ruediste/battery-analyzer/firmware/src/batteryChannelHal_arduino.cpp

#include "config.h"

#if IS_FRAMEWORK_ARDUINO
#include "batteryChannelHal.h"
#include "utils.h"
#include "batteryChannel.h"
#include <Arduino.h>

#if IS_STM
#include <stm32f1xx_ll_tim.h>
#include "stm32f1xx_ll_bus.h"
#endif

void BatteryChannelHal::loop()
{
}

#if IS_AVR
void BatteryChannelHal::setOutputPWM(uint16_t value)
{
  switch (channel)
  {
  case 0:
    OCR1A = value;
    break;
  case 1:
    OCR1B = value;
    break;
  }
}
uint16_t BatteryChannelHal::readVoltage()
{
  // A0/A1

  // select ADC channel with safety mask
  ADMUX = (ADMUX & 0xF0) | (channel & 0x0F);

  // single conversion mode
  ADCSRA |= (1 << ADSC);

  // wait until ADC conversion is complete
  while (ADCSRA & (1 << ADSC))
    ;

  return ADC << 6;
}

void BatteryChannelHal::init()
{
  OCR1A = 0; // clear PWM output
  OCR1B = 0; // clear PWM output

  DDRB |= _BV(PB1) | _BV(PB2);                  // Set pins as outputs (PB1/D9)
  TCCR1A = _BV(COM1A1) | _BV(COM1B1)            // Non-Inv PWM
           | _BV(WGM11);                        // Mode 14: Fast PWM, TOP=ICR1
  TCCR1B = _BV(WGM13) | _BV(WGM12) | _BV(CS10); // Prescaler 1
  ICR1 = 0xffff;                                // TOP counter value (Relieving OCR1A*)

  // adc initialization
  // Select Vref=AVcc
  ADMUX |= (1 << REFS0);

  // set prescaller to 128 and enable ADC (16MHz/128 => 125kHz (should be in range 50kHz to 200 kHz))
  ADCSRA |= (1 << ADPS2) | (1 << ADPS1) | (1 << ADPS0) | (1 << ADEN);
}
#endif

#if IS_STM

TIM_HandleTypeDef htim1;
TIM_HandleTypeDef htim2;
TIM_HandleTypeDef htim3;

void HAL_TIM_MspPostInit(TIM_HandleTypeDef *htim)
{
  GPIO_InitTypeDef GPIO_InitStruct = {0};
  if (htim->Instance == TIM1)
  {
    __HAL_RCC_GPIOA_CLK_ENABLE();
    /**TIM1 GPIO Configuration
    PA8     ------> TIM1_CH1
    PA9     ------> TIM1_CH2
    PA10     ------> TIM1_CH3
    */
    GPIO_InitStruct.Pin = GPIO_PIN_8 | GPIO_PIN_9 | GPIO_PIN_10;
    GPIO_InitStruct.Mode = GPIO_MODE_AF_PP;
    GPIO_InitStruct.Speed = GPIO_SPEED_FREQ_LOW;
    HAL_GPIO_Init(GPIOA, &GPIO_InitStruct);

  }
  else if (htim->Instance == TIM2)
  {
    __HAL_RCC_GPIOB_CLK_ENABLE();
    __HAL_RCC_GPIOA_CLK_ENABLE();
    /**TIM2 GPIO Configuration
    PB10     ------> TIM2_CH3
    PB11     ------> TIM2_CH4
    PA15     ------> TIM2_CH1
    PB3     ------> TIM2_CH2
    */
    GPIO_InitStruct.Pin = GPIO_PIN_10 | GPIO_PIN_11 | GPIO_PIN_3;
    GPIO_InitStruct.Mode = GPIO_MODE_AF_PP;
    GPIO_InitStruct.Speed = GPIO_SPEED_FREQ_LOW;
    HAL_GPIO_Init(GPIOB, &GPIO_InitStruct);

    GPIO_InitStruct.Pin = GPIO_PIN_15;
    GPIO_InitStruct.Mode = GPIO_MODE_AF_PP;
    GPIO_InitStruct.Speed = GPIO_SPEED_FREQ_LOW;
    HAL_GPIO_Init(GPIOA, &GPIO_InitStruct);

    __HAL_AFIO_REMAP_TIM2_ENABLE();

  }
  else if (htim->Instance == TIM3)
  {
    __HAL_RCC_GPIOB_CLK_ENABLE();
    /**TIM3 GPIO Configuration
    PB1     ------> TIM3_CH4
    PB4     ------> TIM3_CH1
    */
    GPIO_InitStruct.Pin = GPIO_PIN_1 | GPIO_PIN_4;
    GPIO_InitStruct.Mode = GPIO_MODE_AF_PP;
    GPIO_InitStruct.Speed = GPIO_SPEED_FREQ_LOW;
    HAL_GPIO_Init(GPIOB, &GPIO_InitStruct);

    __HAL_AFIO_REMAP_TIM3_PARTIAL();

  }
}

/**
 * @brief TIM1 Initialization Function
 * @param None
 * @retval None
 */
static void MX_TIM1_Init(void)
{

  TIM_ClockConfigTypeDef sClockSourceConfig = {0};
  TIM_MasterConfigTypeDef sMasterConfig = {0};
  TIM_OC_InitTypeDef sConfigOC = {0};
  TIM_BreakDeadTimeConfigTypeDef sBreakDeadTimeConfig = {0};

  htim1.Instance = TIM1;
  htim1.Init.Prescaler = 0;
  htim1.Init.CounterMode = TIM_COUNTERMODE_UP;
  htim1.Init.Period = BatteryChannelHal::MAX_PWM;
  htim1.Init.ClockDivision = TIM_CLOCKDIVISION_DIV1;
  htim1.Init.RepetitionCounter = 0;
  htim1.Init.AutoReloadPreload = TIM_AUTORELOAD_PRELOAD_ENABLE;
  if (HAL_TIM_Base_Init(&htim1) != HAL_OK)
  {
    Error_Handler();
  }
  sClockSourceConfig.ClockSource = TIM_CLOCKSOURCE_INTERNAL;
  if (HAL_TIM_ConfigClockSource(&htim1, &sClockSourceConfig) != HAL_OK)
  {
    Error_Handler();
  }
  if (HAL_TIM_PWM_Init(&htim1) != HAL_OK)
  {
    Error_Handler();
  }
  sMasterConfig.MasterOutputTrigger = TIM_TRGO_RESET;
  sMasterConfig.MasterSlaveMode = TIM_MASTERSLAVEMODE_DISABLE;
  if (HAL_TIMEx_MasterConfigSynchronization(&htim1, &sMasterConfig) != HAL_OK)
  {
    Error_Handler();
  }
  sConfigOC.OCMode = TIM_OCMODE_PWM1;
  sConfigOC.Pulse = 0;
  sConfigOC.OCPolarity = TIM_OCPOLARITY_HIGH;
  sConfigOC.OCNPolarity = TIM_OCNPOLARITY_HIGH;
  sConfigOC.OCFastMode = TIM_OCFAST_DISABLE;
  sConfigOC.OCIdleState = TIM_OCIDLESTATE_RESET;
  sConfigOC.OCNIdleState = TIM_OCNIDLESTATE_RESET;
  if (HAL_TIM_PWM_ConfigChannel(&htim1, &sConfigOC, TIM_CHANNEL_1) != HAL_OK)
  {
    Error_Handler();
  }
  if (HAL_TIM_PWM_ConfigChannel(&htim1, &sConfigOC, TIM_CHANNEL_2) != HAL_OK)
  {
    Error_Handler();
  }
  if (HAL_TIM_PWM_ConfigChannel(&htim1, &sConfigOC, TIM_CHANNEL_3) != HAL_OK)
  {
    Error_Handler();
  }
  sBreakDeadTimeConfig.OffStateRunMode = TIM_OSSR_DISABLE;
  sBreakDeadTimeConfig.OffStateIDLEMode = TIM_OSSI_DISABLE;
  sBreakDeadTimeConfig.LockLevel = TIM_LOCKLEVEL_OFF;
  sBreakDeadTimeConfig.DeadTime = 0;
  sBreakDeadTimeConfig.BreakState = TIM_BREAK_DISABLE;
  sBreakDeadTimeConfig.BreakPolarity = TIM_BREAKPOLARITY_HIGH;
  sBreakDeadTimeConfig.AutomaticOutput = TIM_AUTOMATICOUTPUT_DISABLE;
  if (HAL_TIMEx_ConfigBreakDeadTime(&htim1, &sBreakDeadTimeConfig) != HAL_OK)
  {
    Error_Handler();
  }
  HAL_TIM_MspPostInit(&htim1);
}

/**
 * @brief TIM2 Initialization Function
 * @param None
 * @retval None
 */
static void MX_TIM2_Init(void)
{

  TIM_ClockConfigTypeDef sClockSourceConfig = {0};
  TIM_MasterConfigTypeDef sMasterConfig = {0};
  TIM_OC_InitTypeDef sConfigOC = {0};

  htim2.Instance = TIM2;
  htim2.Init.Prescaler = 0;
  htim2.Init.CounterMode = TIM_COUNTERMODE_UP;
  htim2.Init.Period = BatteryChannelHal::MAX_PWM;
  htim2.Init.ClockDivision = TIM_CLOCKDIVISION_DIV1;
  htim2.Init.AutoReloadPreload = TIM_AUTORELOAD_PRELOAD_ENABLE;
  if (HAL_TIM_Base_Init(&htim2) != HAL_OK)
  {
    Error_Handler();
  }
  sClockSourceConfig.ClockSource = TIM_CLOCKSOURCE_INTERNAL;
  if (HAL_TIM_ConfigClockSource(&htim2, &sClockSourceConfig) != HAL_OK)
  {
    Error_Handler();
  }
  if (HAL_TIM_PWM_Init(&htim2) != HAL_OK)
  {
    Error_Handler();
  }
  sMasterConfig.MasterOutputTrigger = TIM_TRGO_RESET;
  sMasterConfig.MasterSlaveMode = TIM_MASTERSLAVEMODE_DISABLE;
  if (HAL_TIMEx_MasterConfigSynchronization(&htim2, &sMasterConfig) != HAL_OK)
  {
    Error_Handler();
  }
  sConfigOC.OCMode = TIM_OCMODE_PWM1;
  sConfigOC.Pulse = 0;
  sConfigOC.OCPolarity = TIM_OCPOLARITY_HIGH;
  sConfigOC.OCFastMode = TIM_OCFAST_DISABLE;
  if (HAL_TIM_PWM_ConfigChannel(&htim2, &sConfigOC, TIM_CHANNEL_1) != HAL_OK)
  {
    Error_Handler();
  }
  if (HAL_TIM_PWM_ConfigChannel(&htim2, &sConfigOC, TIM_CHANNEL_2) != HAL_OK)
  {
    Error_Handler();
  }
  if (HAL_TIM_PWM_ConfigChannel(&htim2, &sConfigOC, TIM_CHANNEL_3) != HAL_OK)
  {
    Error_Handler();
  }
  if (HAL_TIM_PWM_ConfigChannel(&htim2, &sConfigOC, TIM_CHANNEL_4) != HAL_OK)
  {
    Error_Handler();
  }
  HAL_TIM_MspPostInit(&htim2);
}

/**
 * @brief TIM3 Initialization Function
 * @param None
 * @retval None
 */
static void MX_TIM3_Init(void)
{

  TIM_ClockConfigTypeDef sClockSourceConfig = {0};
  TIM_MasterConfigTypeDef sMasterConfig = {0};
  TIM_OC_InitTypeDef sConfigOC = {0};

  htim3.Instance = TIM3;
  htim3.Init.Prescaler = 0;
  htim3.Init.CounterMode = TIM_COUNTERMODE_UP;
  htim3.Init.Period = BatteryChannelHal::MAX_PWM;
  htim3.Init.ClockDivision = TIM_CLOCKDIVISION_DIV1;
  htim3.Init.AutoReloadPreload = TIM_AUTORELOAD_PRELOAD_ENABLE;
  if (HAL_TIM_Base_Init(&htim3) != HAL_OK)
  {
    Error_Handler();
  }
  sClockSourceConfig.ClockSource = TIM_CLOCKSOURCE_INTERNAL;
  if (HAL_TIM_ConfigClockSource(&htim3, &sClockSourceConfig) != HAL_OK)
  {
    Error_Handler();
  }
  if (HAL_TIM_PWM_Init(&htim3) != HAL_OK)
  {
    Error_Handler();
  }
  sMasterConfig.MasterOutputTrigger = TIM_TRGO_RESET;
  sMasterConfig.MasterSlaveMode = TIM_MASTERSLAVEMODE_DISABLE;
  if (HAL_TIMEx_MasterConfigSynchronization(&htim3, &sMasterConfig) != HAL_OK)
  {
    Error_Handler();
  }
  sConfigOC.OCMode = TIM_OCMODE_PWM1;
  sConfigOC.Pulse = 0;
  sConfigOC.OCPolarity = TIM_OCPOLARITY_HIGH;
  sConfigOC.OCFastMode = TIM_OCFAST_DISABLE;
  if (HAL_TIM_PWM_ConfigChannel(&htim3, &sConfigOC, TIM_CHANNEL_1) != HAL_OK)
  {
    Error_Handler();
  }
  if (HAL_TIM_PWM_ConfigChannel(&htim3, &sConfigOC, TIM_CHANNEL_4) != HAL_OK)
  {
    Error_Handler();
  }
  HAL_TIM_MspPostInit(&htim3);
}

// int BatteryChannelHal::pwmPins[] = {PA8, PA9, PB11, PB1, PA10, PA15, PB3, PB4};
int BatteryChannelHal::analogInPins[] = {PA0, PA1, PA2, PA3, PA4, PA5, PA6, PA7};

void BatteryChannelHal::setOutputPWM(uint16_t value)
{
  // analogWrite(pwmPins[channel], value);
  switch (channel)
  {
  case 0: // PA8
    htim1.Instance->CCR1 = value;
    break;
  case 1: // PA9
    htim1.Instance->CCR2 = value;
    break;
  case 2: // PB11
    htim2.Instance->CCR4 = value;
    break;
  case 3: // PB1
    htim3.Instance->CCR4 = value;
    break;
  case 4: // PA10
    htim1.Instance->CCR3 = value;
    break;
  case 5: // PA15
    htim2.Instance->CCR1 = value;
    break;
  case 6: // PB3
    htim2.Instance->CCR2 = value;
    break;
  case 7: // PB4
    htim3.Instance->CCR1 = value;
    break;
  }
}

uint16_t BatteryChannelHal::readVoltage()
{
  return analogRead(analogInPins[channel]);
}

void BatteryChannelHal::init()
{
  MX_TIM1_Init();
  MX_TIM2_Init();
  MX_TIM3_Init();

  HAL_TIM_PWM_Start(&htim1, TIM_CHANNEL_1);
  HAL_TIM_PWM_Start(&htim1, TIM_CHANNEL_2);
  HAL_TIM_PWM_Start(&htim2, TIM_CHANNEL_4);
  HAL_TIM_PWM_Start(&htim3, TIM_CHANNEL_4);
  HAL_TIM_PWM_Start(&htim1, TIM_CHANNEL_3);
  HAL_TIM_PWM_Start(&htim2, TIM_CHANNEL_1);
  HAL_TIM_PWM_Start(&htim2, TIM_CHANNEL_2);
  HAL_TIM_PWM_Start(&htim3, TIM_CHANNEL_1);

  // ref
  HAL_TIM_PWM_Start(&htim2, TIM_CHANNEL_3);
  htim2.Instance->CCR3 = MAX_PWM >> 1;

  // analogWriteFrequency(10000);
  // analogWriteResolution(12);

  analogReadResolution(16);

  // analogWrite(PB10, 0x400);
  // AFIO->MAPR2|=AFIO_MAPR_TIM2_REMAP_FULLREMAP;

  for (int i = 0; i < channelCount; i++)
    pinMode(analogInPins[i], INPUT_ANALOG);
  // for (int i = 0; i < channelCount; i++)
  //     pinMode(pwmPins[i], OUTPUT);
}
#endif
#endif
