ruediste/battery-analyzer/firmware/src/input_native.cpp

#define INPUT_CPP
#include "config.h"

#if IS_FRAMEWORK_NATIVE
#include "input.h"
#include "utils.h"

namespace input
{
  void init()
  {
    // NOOP
  }

  void loop()
  {
    // NOOP
  }
  void checkInputs()
  {
    // NOOP
  }

} // namespace Input

#endif
