ruediste/battery-analyzer/cubeMx/test.ioc

Mcu.UserName=STM32F103C8Tx
PA0-WKUP.Signal=ADCx_IN0
PA1.Signal=ADCx_IN1
PA10.Signal=S_TIM1_CH3
PA15.Signal=S_TIM2_CH1_ETR
PA2.Signal=ADCx_IN2
PA3.Signal=ADCx_IN3
PA4.Signal=ADCx_IN4
PA5.Signal=ADCx_IN5
PA6.Signal=ADCx_IN6
PA7.Signal=ADCx_IN7
PA8.Signal=S_TIM1_CH1
PA9.Signal=S_TIM1_CH2
PB1.Signal=S_TIM3_CH4
PB10.Signal=S_TIM2_CH3
PB11.Signal=S_TIM2_CH4
PB12.Signal=GPIO_Input
PB13.Signal=SPI2_SCK
PB14.Signal=SPI2_MISO
PB15.Signal=SPI2_MOSI
PB3.Signal=S_TIM2_CH2
PB4.Signal=S_TIM3_CH1
PB6.Signal=I2C1_SCL
PB7.Signal=I2C1_SDA
PB8.Signal=GPIO_Input
PB9.Signal=GPIO_Input
